yasenOfficial/ZekEng-Intern/Files for Reverse Engineering/Screenshot 2025-05-29 131428.jpg

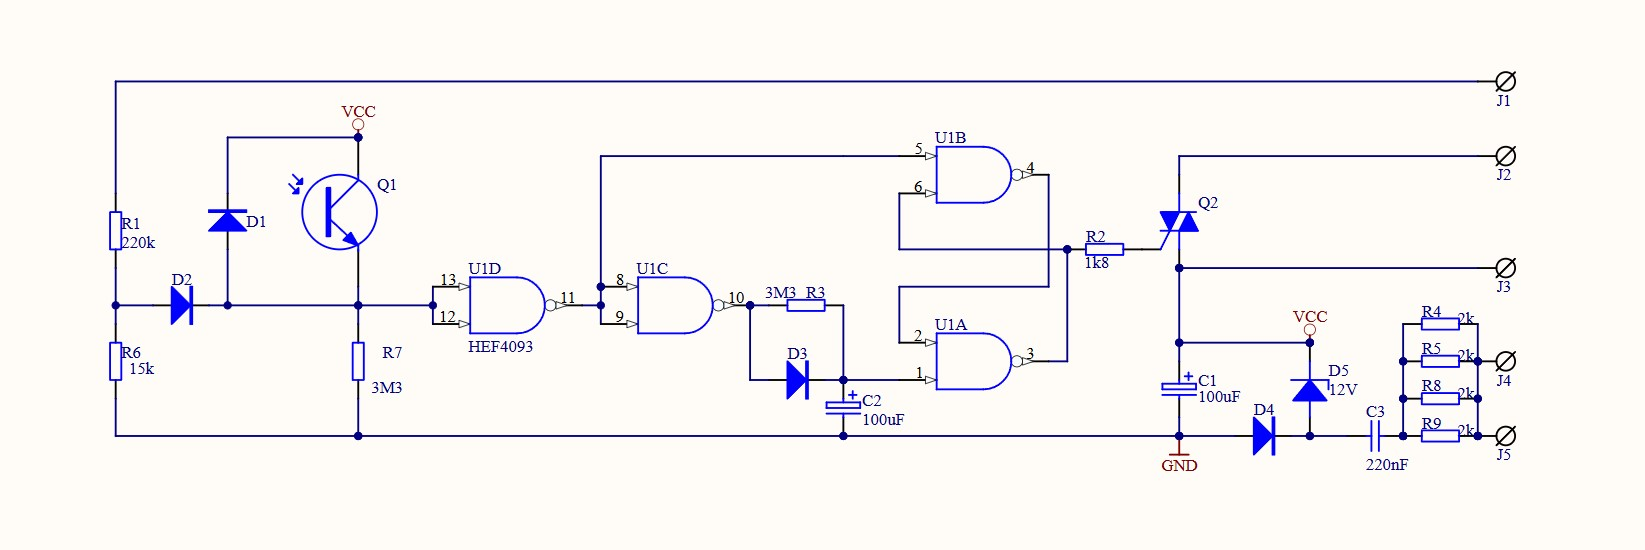
Files for Reverse Engineering/Screenshot 2025-05-29 131428.jpg
