yasenOfficial/ZekEng-Intern/Files for Reverse Engineering/Screenshot 2025-05-29 131514.jpg

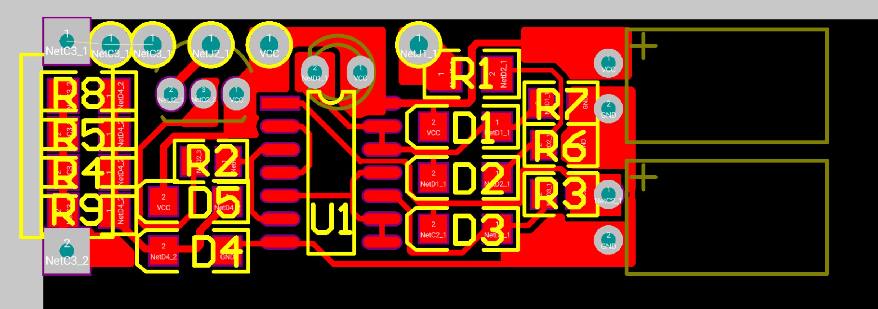
Files for Reverse Engineering/Screenshot 2025-05-29 131514.jpg
