yasenOfficial/ZekEng-Intern/Images/HR202.jpg

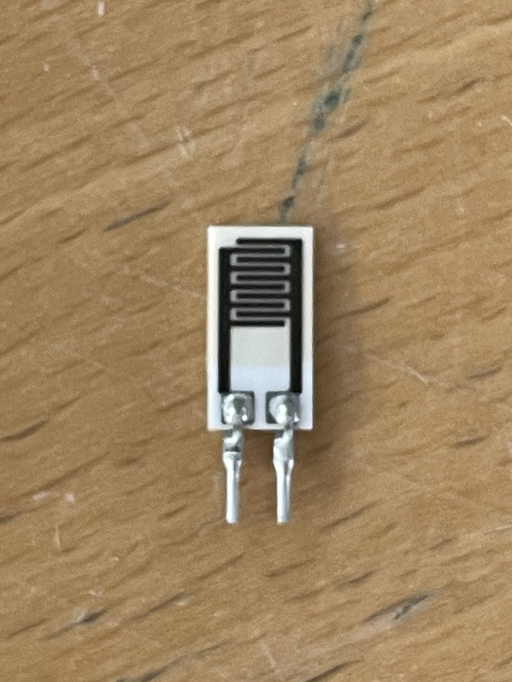
Images/HR202.jpg
