yasenOfficial/ZekEng-Intern/Images/PMUTokNaResistorite.png

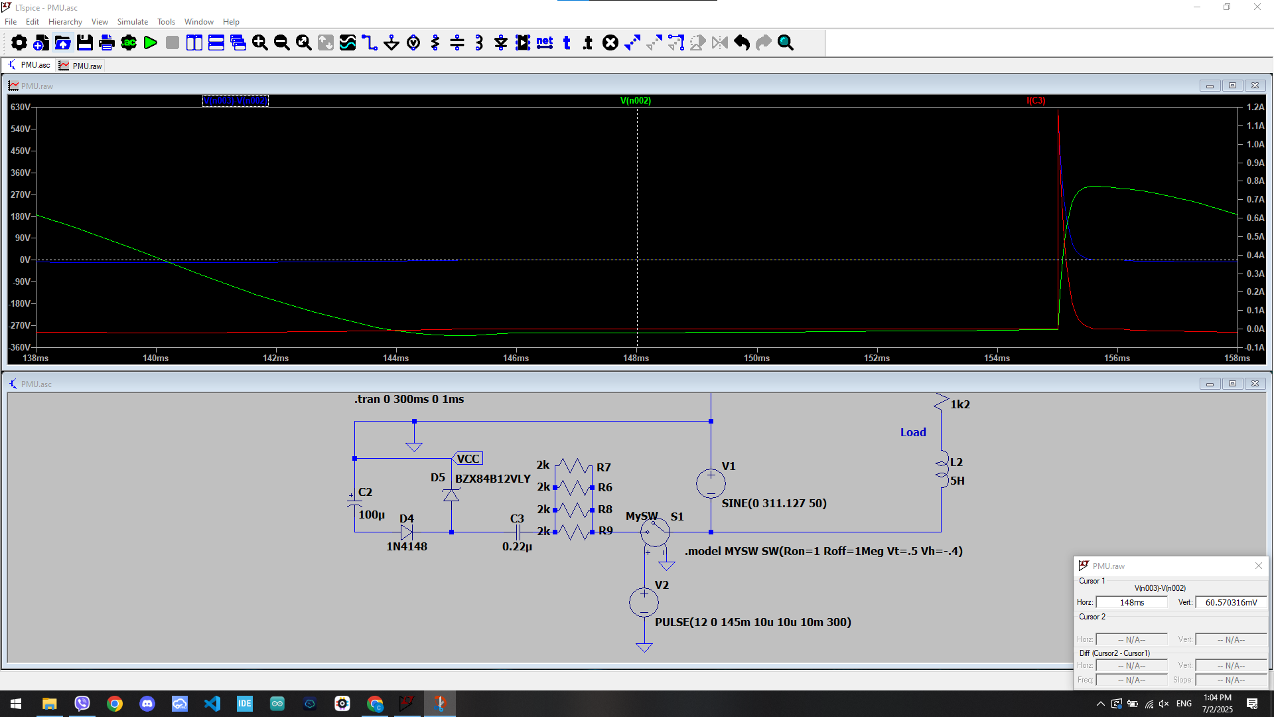
Images/PMUTokNaResistorite.png
