yasenOfficial/ZekEng-Intern/DaisyExamples/patch_sm/GettingStarted/Audio_Settings/README.md

# Audio_Settings

## Author

beserge

## Description

Audio passthrough with audio setting adjustment.  
Samplerate = 16kHz. Blocksize = 4 samples.  
For help connecting the jacks, refer to figures 1.1 and 1.8 in the [Patch SM Datasheet](https://github.com/electro-smith/DaisyPatchSM/blob/main/doc/datasheet/ES_Patch_SM_datasheet_v1.0.pdf).  

## Controls

| Pin Name | Pin Location | Comment |
| --- | --- | --- |
| Audio Out Right | B1 | Connect this to an audio jack's signal leg. |
| Audio Out Left | B2 | Connect this to an audio jack's signal leg. |
| Audio In Right | B3 | Connect this to an audio jack's signal leg. |
| Audio In Left | B4 | Connect this to an audio jack's signal leg. |
| GND | A7 | Connect this all of your audio jacks' ground legs. |
