yasenOfficial/ZekEng-Intern/DaisyExamples/patch_sm/GettingStarted/CV_Input/README.md

# CV_Input

## Author

beserge

## Description

Turns the onboard led on or off based on CV. If the CV input is positive, the led is on.  
If the CV input is negative, the LED is off. Uses CV_1.
For help connecting the CV input jack, refer to figure 1.3 in the [Patch SM Datasheet](https://github.com/electro-smith/DaisyPatchSM/blob/main/doc/datasheet/ES_Patch_SM_datasheet_v1.0.pdf).  

## Controls

| Pin Name | Pin Location | Function |
| --- | --- | --- |
| CV 1 | C5 | CV In |
