yasenOfficial/ZekEng-Intern/DaisyExamples/patch_sm/GettingStarted/Momentary_Switch/README.md

# Momentary_Switch

## Author

beserge

## Description

Set the onboard led to the state off a momentary switch.
For help connecting the momentary switch, refer to figure 1.5 in the [Patch SM Datasheet](https://github.com/electro-smith/DaisyPatchSM/blob/main/doc/datasheet/ES_Patch_SM_datasheet_v1.0.pdf).  

| Pin Name | Pin Location | Function | Comment |
| --- | --- | --- | --- |
| B7 | B7 | Switch In | Connect this to any leg of the switch |
| GND | A4 | Switch Ground | Connect this to the leg diagonally across from Switch In |
