yasenOfficial/ZekEng-Intern/DaisyExamples/patch_sm/GettingStarted/Pot_Input/README.md

# Pot_Input

## Author

beserge

## Description

Set the onboard led's brightness with a potentiometer.
For help connecting the potentiometer, refer to figure 1.2 in the [Patch SM Datasheet](https://github.com/electro-smith/DaisyPatchSM/blob/main/doc/datasheet/ES_Patch_SM_datasheet_v1.0.pdf).  

## Controls

| Pin Name | Pin Location | Function | Comment |
| --- | --- | --- | --- |
| CV 1 | C5 | Pot In | Connect this to the pot's middle leg |
| 5V | A6 | Pot Supply Voltage | Connect this to the pot's right leg |
| GND | A4 | Pot Ground | Connect this to the pot's left leg |
