yasenOfficial/ZekEng-Intern/DaisyExamples/patch_sm/GettingStarted/Toggle_Switch/README.md

# Toggle_Switch

## Author

beserge

## Description

Set the onboard led based on a toggle switch.
For help connecting the toggle switch, refer to figure 1.6 in the [Patch SM Datasheet](https://github.com/electro-smith/DaisyPatchSM/blob/main/doc/datasheet/ES_Patch_SM_datasheet_v1.0.pdf).  

## Controls

| Pin Name | Pin Location | Function | Comment |
| --- | --- | --- | --- |
| B8 | B8 | Toggle In | Connect this the switch's middle leg. |
| GND | A7 | Toggle Ground | Connect this to one of the switch's outer legs |
