yasenOfficial/ZekEng-Intern/LTSpice Files/TutorialRoman.asc

Q1: npn; 2N2222
Q2: pnp; 2N2907
R1: res; 100k
R2: res; 10k
R3: res; 10k
R4: res; 1k
U1: UniversalOpAmp2
V1: voltage; ""; AC 1
V2: voltage; 15
V3: voltage; 15
Named nets: 0, Out
