yasenOfficial/ZekEng-Intern/LTSpice Files/Ventilator/NAND Tests.asc

U3: CD4093B
V1: voltage; SINE(6 6 50)
Named nets: 0, OUT
.include lib/sub/CD4000.lib
.tran 0.5
