yasenOfficial/ZekEng-Intern/LTSpice Files/TutorialRoman/TutorialRoman.asc

Q1: npn; 2N2222
Q2: pnp; 2N2907
R1: res; {Rgain}
R2: res; 10k
R3: res; 10k
R4: res; 1k
U1: UniversalOpAmp2
V1: voltage; SINE(0 1 50k); AC 1
V2: voltage; 15
V3: voltage; 15
Named nets: 0, Out
.ac dec 50 1k 10Meg
.tran 0 300u 100u 0.01u
.four 500k 10V(out)
.step lin param Rgain 100k 200k 20k
