yasenOfficial/ZekEng-Intern/LTSpice Files/Ventilator/PMU.asc

C2: polcap; 100µ; V=16 Irms=280m Rser=0.11 Lser=3.5n mfg="Würth Elektronik" pn="860040373002 WCAP-ATUL 6,3x11" type="Al electrolytic"
C3: cap; 0.22µ; V=400 Irms=0 Rser=0.0381 Lser=11.951n mfg="Würth Elektronik" pn="890283425002CS WCAP-FTBE 15 x 18 x 11 x 5" type="Box"
D4: diode; 1N4148
D5: zener; BZX84B12VLY
L2: ind; 5H
R1: res; 130R
R2: res; 130R
R3: res; 130R
R4: res; 130R
RL: res; 1k2
S1: sw; MySW
V1: voltage; SINE(0 311.127 50)
V2: voltage; PULSE(12 0 145m 10u 10u 10m 300)
Named nets: VCC, 0
.tran 0 300ms 0 1ms
.include lib/sub/thyristr.lib
.include lib/sub/CD4000.lib
.sympath lib/sym
Load
.model MYSW SW(Ron=1 Roff=1Meg Vt=.5 Vh=-.4)
