yasenOfficial/ZekEng-Intern/LTSpice Files/Ventilator/Ventilator.asc

C1: polcap; 100µ; V=16 Irms=280m Rser=0.11 Lser=3.5n mfg="Würth Elektronik" pn="860040373002 WCAP-ATUL 6,3x11" type="Al electrolytic"
C2: polcap; 100µ; V=16 Irms=280m Rser=0.11 Lser=3.5n mfg="Würth Elektronik" pn="860040373002 WCAP-ATUL 6,3x11" type="Al electrolytic"
C3: cap; 0.22µ; V=400 Irms=0 Rser=0.0381 Lser=11.951n mfg="Würth Elektronik" pn="890283425002CS WCAP-FTBE 15 x 18 x 11 x 5" type="Box"
D1: diode; 1N4148
D2: diode; 1N4148
D3: diode; 1N4148
D4: diode; 1N4148
D5: zener; BZX84B12VLY
L2: ind; 5H
R1: res; 220K
R2: res; 15K
R3: res; 3m3
R4: res; 3Meg3
R5: res; 1k8
R6: res; 2k
R7: res; 2k
R8: res; 2k
R9: res; 2k
R10: res; 10K
R11: res; 10K
RL: res; 1k2
Rsw2: res; {RPWR}
Rsw: res; {RHumSensor}
S1: sw; HumSensor
S3: sw; SWPWR
U1: TRIAC; MAC97A8
U2: CD4093B; VDD=12 SPEED=1.0 TRIPDT=5e-9
U3: CD4093B; VDD=12 SPEED=1.0 TRIPDT=5e-9
U4: CD4093B; VDD=12 SPEED=1.0 TRIPDT=5e-9
U5: CD4093B; VDD=12 SPEED=1.0 TRIPDT=5e-9
V1: voltage; SINE(0 311.127 50)
Named nets: VCC, 0
.model HumSensor SW(Ron=1 Roff=1Meg Vt=2.5 Vh=0)...
.step param RHumSensor list 1 1e6...
.tran 0 150u 50u 1u
.include lib/sub/thyristr.lib
.include lib/sub/CD4000.lib
.sympath lib/sym
.step param RPWR list 1 1e6
.model SWPWR SW(Ron=1 Roff=1Meg Vt=2.5 Vh=0)
Load
