yasenOfficial/ZekEng-Intern/LTSpice Files/Ventilator/SW.asc

R1: res; 1K
R2: res; {RSW}
R3: res
S1: sw; MYSW
V1: voltage; 5
V2: voltage; 3.3
Named nets: 0
.model MYSW SW(Ron=1 Roff=1Meg Vt=.5 Vh=-.4)
.tran 0 2ms 0 1u
.step param RSW 0.0000000001 1e6 111111.111
